lilindian16/customDRC/Images/SMPSU/sw_pin_ringing_dp100.png

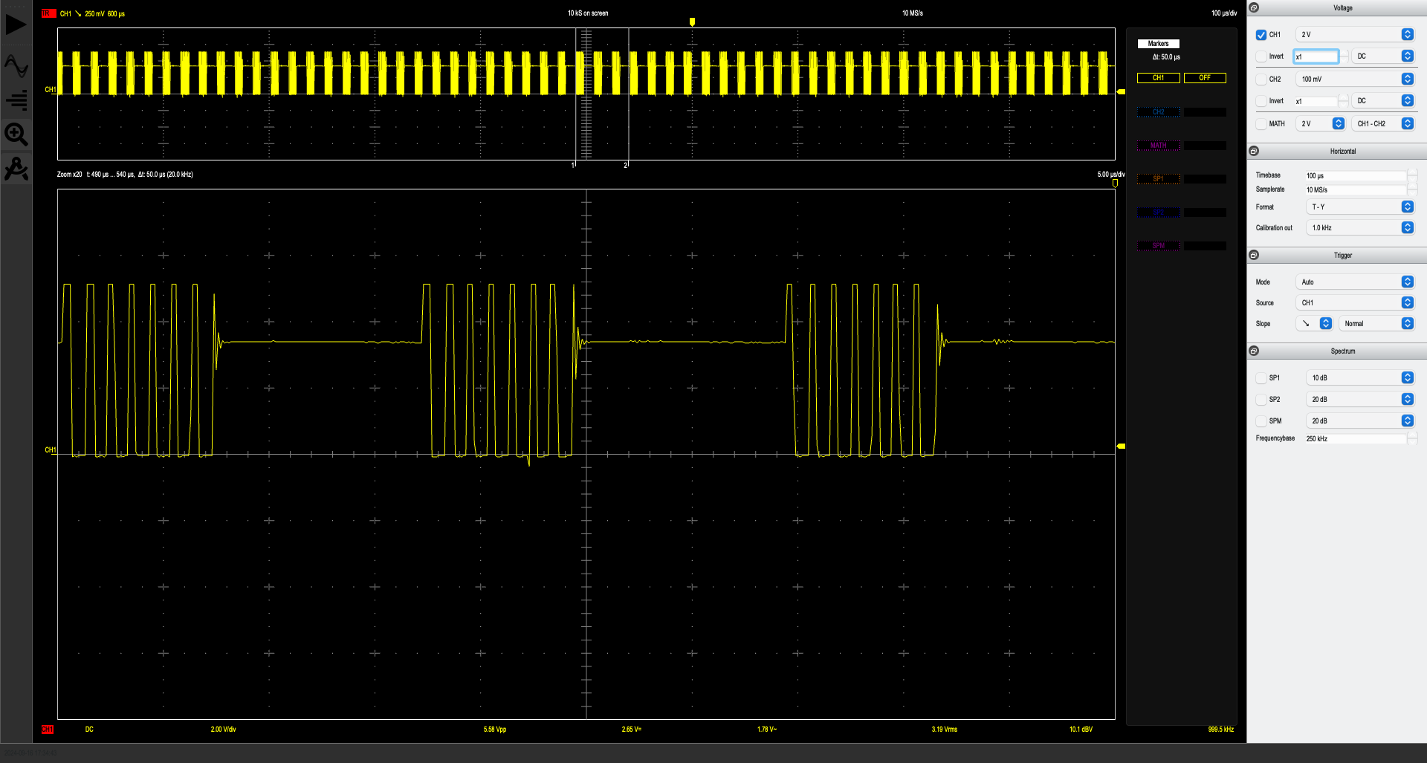
Images/SMPSU/sw_pin_ringing_dp100.png
