lilindian16/customDRC/Images/Software/CDRC_webpage_iPadPro.png

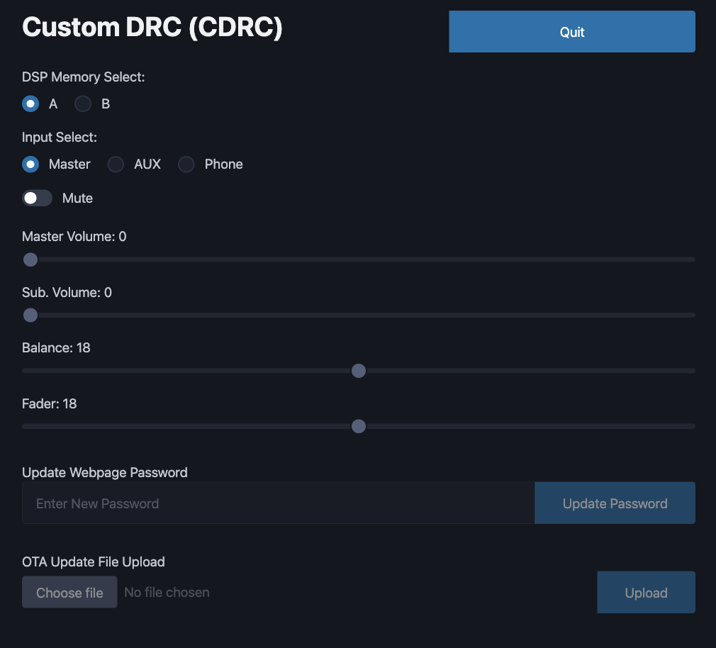
Images/Software/CDRC_webpage_iPadPro.png
