lilindian16/customDRC/Images/Software/CDRC_webpage_iphone12pro.png

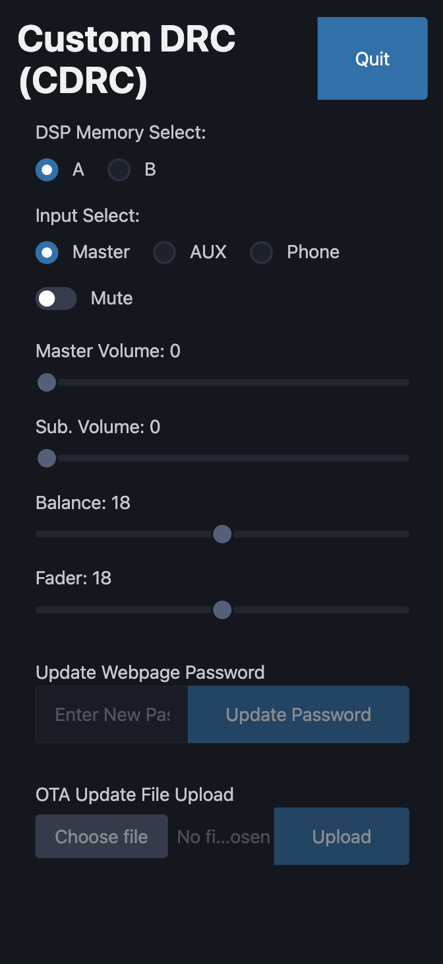
Images/Software/CDRC_webpage_iphone12pro.png
