lilindian16/customDRC/Images/Traces/rs485_bus_capture.png

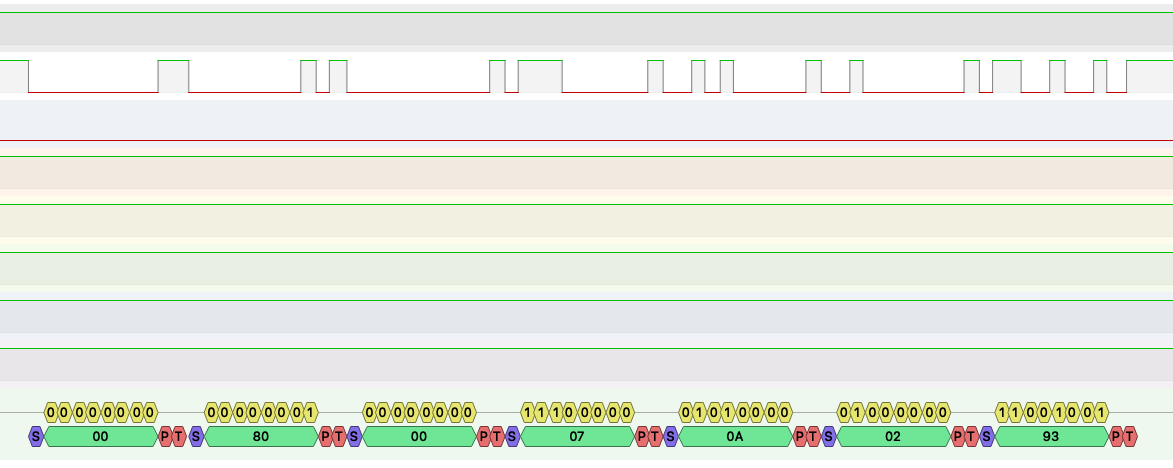
Images/Traces/rs485_bus_capture.png
