lilindian16/customDRC/Images/Traces/volume_adjust_0x00_20240821_082051.png

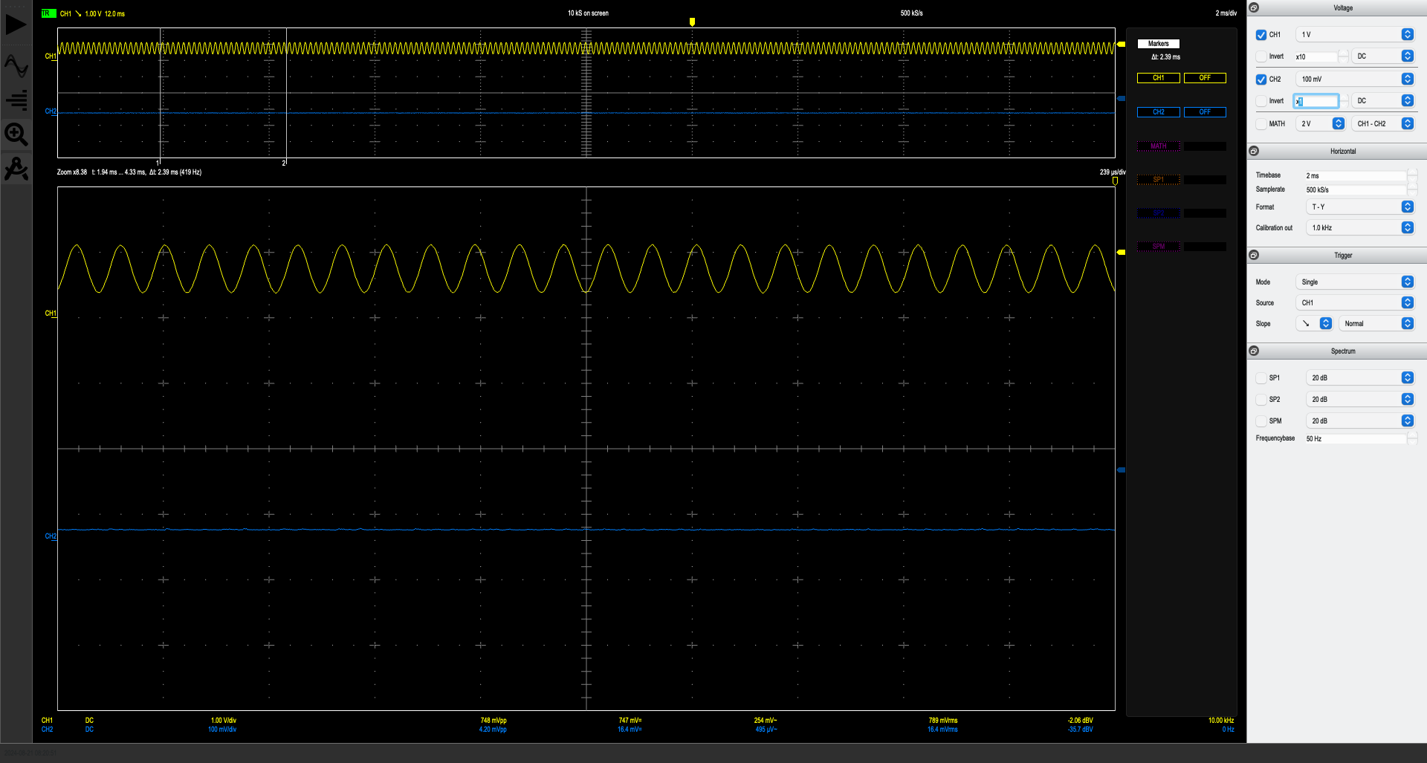
Images/Traces/volume_adjust_0x00_20240821_082051.png
